BKRLearning/NFOI/Juicer/Current/1P/JuicerController_averageValsMultiple.ino

#define JUICER_LEFT 18
#define JUICER_RIGHT 17
#define JUICER_UP 16
#define JUICER_DOWN 15

#define LED_LEFT 4
#define LED_RIGHT 5
#define LED_UP 6
#define LED_DOWN 7

// arrays for juicer pressed/released bools in order L, R, U, D
byte juicersPressed[] = {false, false, false, false};
byte juicersReleased[] = {false, false, false, false};

// arrays for juicer analog readings in order L, R, U, D
uint16_t baselineVals[] = {0, 0, 0, 0};
uint16_t currentVals[] = {0, 0, 0, 0};
uint16_t previousVals[] = {0, 0, 0, 0};

// arrays for pressed juicer running avg values
const byte arraySize = 6;
long pushedVals[4][arraySize];    // 2D array contains 4 arrays with the last "arraySize" readings of each juicer to use for averaging 
byte readIndexes[] = {0, 0, 0, 0};
long totals[] = {0, 0, 0, 0};
float averages[]  = {0, 0, 0, 0};

// setup millis delay
long startMillis;
long currentMillis;
const long period = 7;


void setup() {
  Serial.begin(9600);

  startMillis = millis();

  // fill running avg arrays with zeros
  for (int i = 0; i < 4; i++) {
    for (int j = 0; j < arraySize; j++) {
      pushedVals[i][j] = 0;
    }
  }

  // LED outputs
  pinMode(LED_LEFT, OUTPUT);
  pinMode(LED_RIGHT, OUTPUT);
  pinMode(LED_UP, OUTPUT);
  pinMode(LED_DOWN, OUTPUT);

  // get juicer baseline readings
  baselineVals[0] = analogRead(JUICER_LEFT);
  baselineVals[1] = analogRead(JUICER_RIGHT);
  baselineVals[2] = analogRead(JUICER_UP);
  baselineVals[3] = analogRead(JUICER_DOWN);
}

void loop() {

  currentMillis = millis();
  if (currentMillis - startMillis >= period) {  // run this code every "period" (in ms)

    getVals(); // get current vals for each juicer

    for (int i = 0; i < 4; i++) {
      if (juicersPressed[i]) {  // if a particular juicer was pressed, then...
        totals[i] = totals[i] - pushedVals[i][readIndexes[i]];  // subtract the last value from the running total
        pushedVals[i][readIndexes[i]] = currentVals[i]; // get the new pressed value from the current value array
        totals[i] = totals[i] + pushedVals[i][readIndexes[i]]; // add that value to the running total
        readIndexes[i]++; // update the index

        if (readIndexes[i] >= arraySize) {  // reset the index number once it gets to the max array size
          readIndexes[i] = 0;
        }

        averages[i] = totals[i] / arraySize;
        delay(1);

        if (abs(averages[i] - baselineVals[i]) <= 2) {  // check if the difference between the running avg and the baseline val for any juicer is within 2
          juicersReleased[i] = true;
          juicersPressed[i] = false;
        }
      }
      delay(1);
    }

    startMillis = currentMillis;
  }


  getJuicersPressed();    // check if player has pressed juicer
  getJuicersReleased();   // check if player has released juicer

  delay(1);
}


void getVals() {  // get current values for each juicer
  previousVals[0] = currentVals[0];
  currentVals[0] = analogRead(JUICER_LEFT);

  previousVals[1] = currentVals[1];
  currentVals[1] = analogRead(JUICER_RIGHT);

  previousVals[2] = currentVals[2];
  currentVals[2] = analogRead(JUICER_UP);

  previousVals[3] = currentVals[3];
  currentVals[3] = analogRead(JUICER_DOWN);

  delay(1);
}



void getJuicersPressed() {  // check if player has pressed juicer
  for (int i = 0; i < 4; i++) {
    if (!juicersReleased[i] && abs(previousVals[i] - currentVals[i]) >= 15) { // actively pressing juicer if dif between previous and current val within 15
      juicersPressed[i] = true;

      switch (i) {
        case 0:
          Keyboard.press(KEY_LEFT);
          break;
        case 1:
          Keyboard.press(KEY_RIGHT);
          break;
        case 2:
          Keyboard.press(KEY_UP);
          break;
        case 3:
          Keyboard.press(KEY_DOWN);
          break;
      }
    }
    delay(1);
  }
}

void getJuicersReleased() {  // check if juicer has been released after being pressed
  for (int i = 0; i < 4; i++) {
    if (!juicersPressed[i] && juicersReleased[i]) {
      switch (i) { 
        case 0:
          delay(1);
          Keyboard.release(KEY_LEFT);
          break;
        case 1:
          delay(1);
          Keyboard.release(KEY_RIGHT);
          break;
        case 2:
          delay(1);
          Keyboard.release(KEY_UP);
          break;
        case 3:
          delay(1);
          Keyboard.release(KEY_DOWN);
          break;
      }

      // reset averaging array setup for that juicer
      for (int j = 0; j < arraySize; j++) {
        pushedVals[i][j] = 0;
      }
      totals[i] = 0;

      // reset state vals for that juicer
      juicersPressed[i] = false;
      juicersReleased[i] = false;

    }

    delay(1);
  }
}
